bitaxeorg/bitaxeBIRDS/3d/TXB0104RGYR.STEP

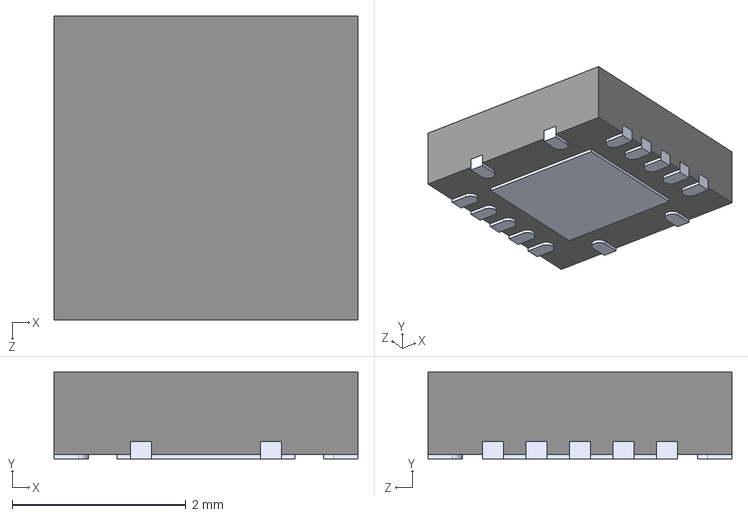
[picture p16: CAD file, 2025-10-02]
3d/TXB0104RGYR.STEP
3.50 x 1.00 x 3.50 mm
