bitaxeorg/bitaxeBIRDS/3d/TPS546D24ARVFR.step

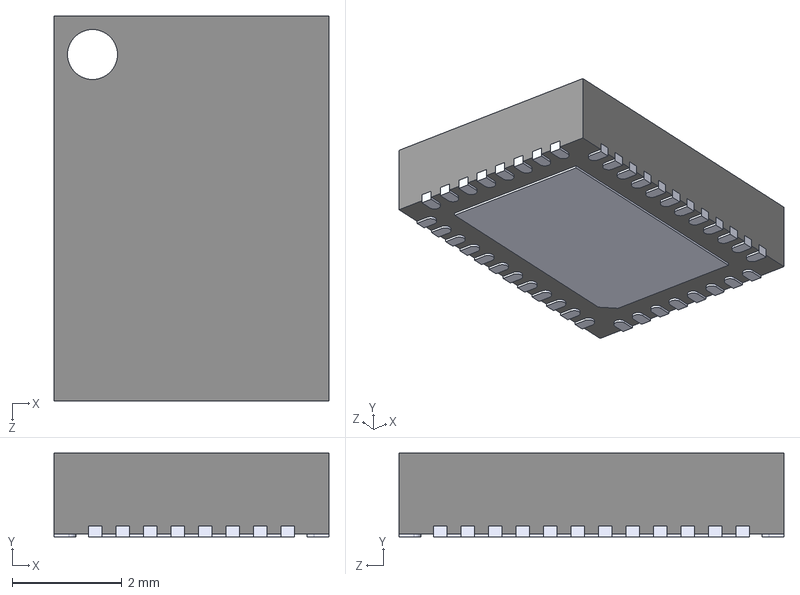
[picture p18: CAD file, 2025-10-02]
3d/TPS546D24ARVFR.step
5.00 x 1.52 x 7.00 mm
