bitaxeorg/bitaxeBIRDS/3d/BitaxeGT_heatsink.step

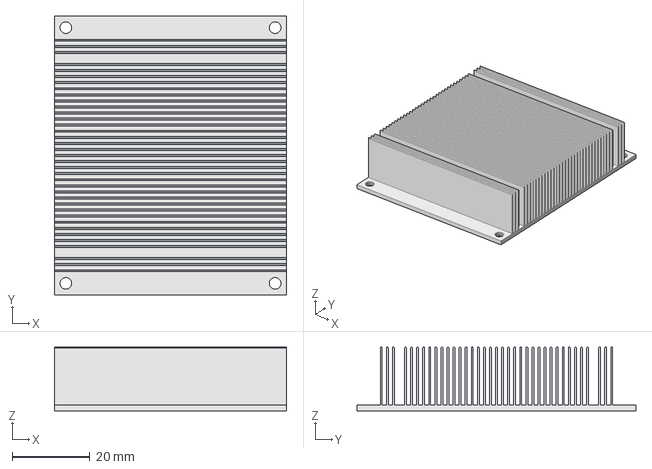
[picture p19: CAD file, 2025-10-02]
3d/BitaxeGT_heatsink.step
60.0 x 72.0 x 16.5 mm
