bitaxeorg/bitaxeBIRDS/3d/BM04B-SRSS-TB.STEP

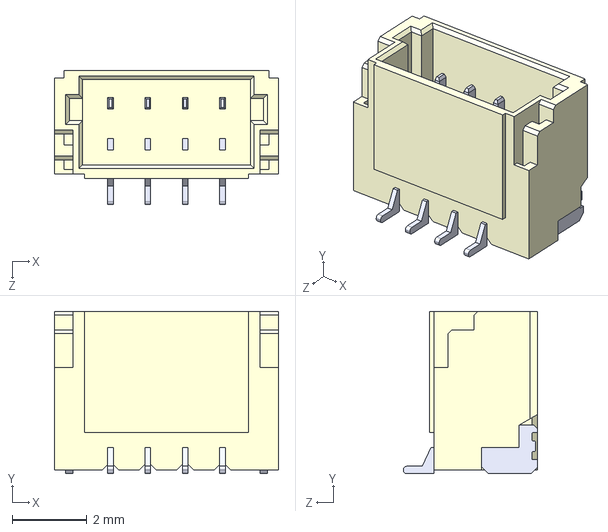
[picture p20: CAD file, 2025-10-02]
3d/BM04B-SRSS-TB.STEP
6.00 x 4.35 x 3.60 mm
