bitaxeorg/bitaxeBIRDS/3d/BM1368xx.stp

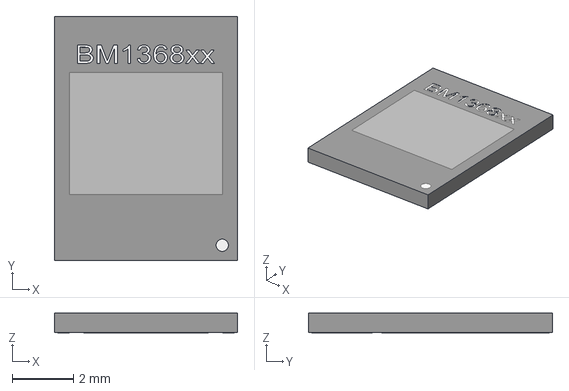
[picture p21: CAD file, 2025-10-02]
3d/BM1368xx.stp
6.00 x 8.00 x 0.65 mm
