bitaxeorg/bitaxeBIRDS/3d/USB_10118193-0001LF.STEP

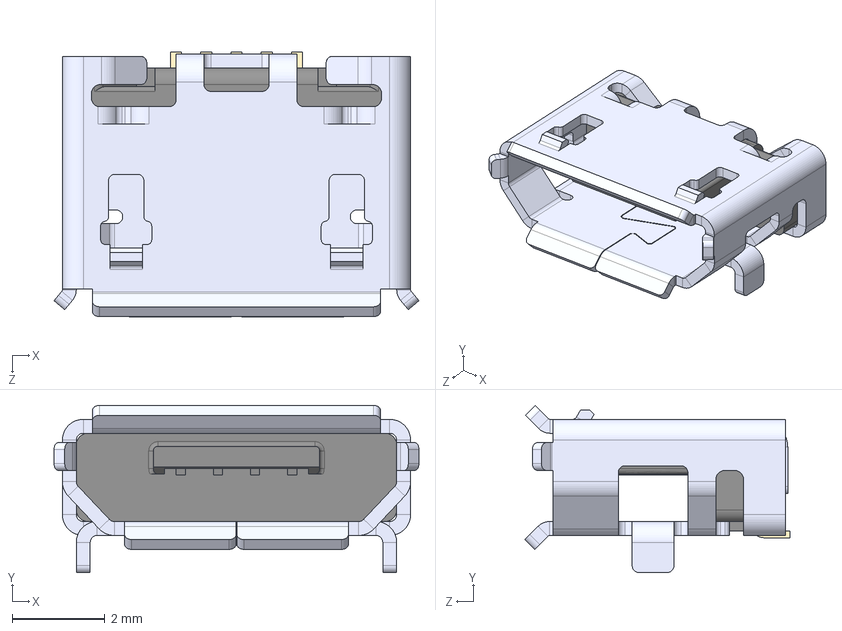
[picture p25: CAD file, 2025-10-02]
3d/USB_10118193-0001LF.STEP
7.86 x 3.60 x 5.71 mm
