bitaxeorg/bitaxeBIRDS/3d/IHLP2020CZ.step

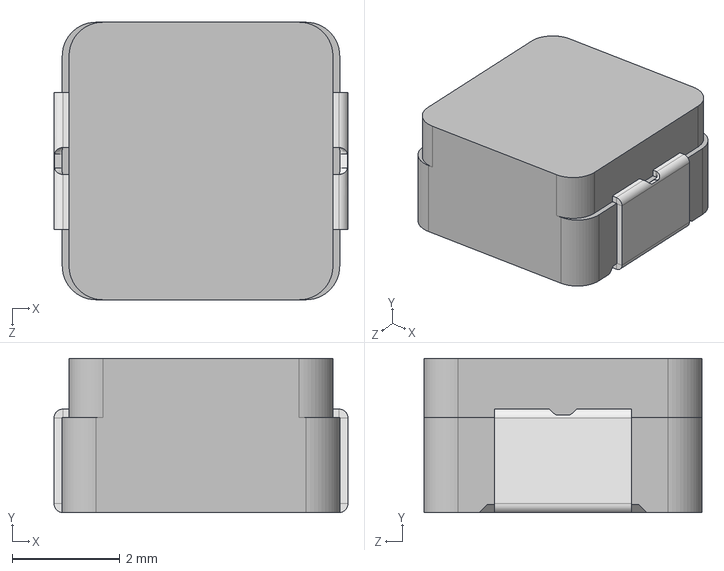
[picture p26: CAD file, 2025-10-02]
3d/IHLP2020CZ.step
5.45 x 2.86 x 5.15 mm
