bitaxeorg/bitaxeBIRDS/3d/TSOT-23-5_RIT.step

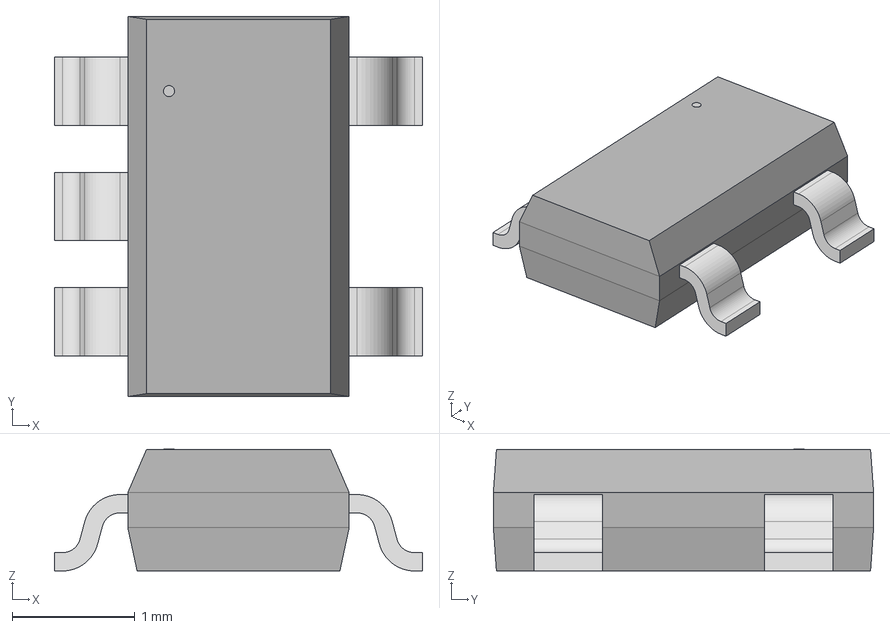
[picture p28: CAD file, 2025-10-02]
3d/TSOT-23-5_RIT.step
3.00 x 3.10 x 0.993 mm
