bitaxeorg/bitaxeBIRDS/3d/FFC2B35-08-T.STEP

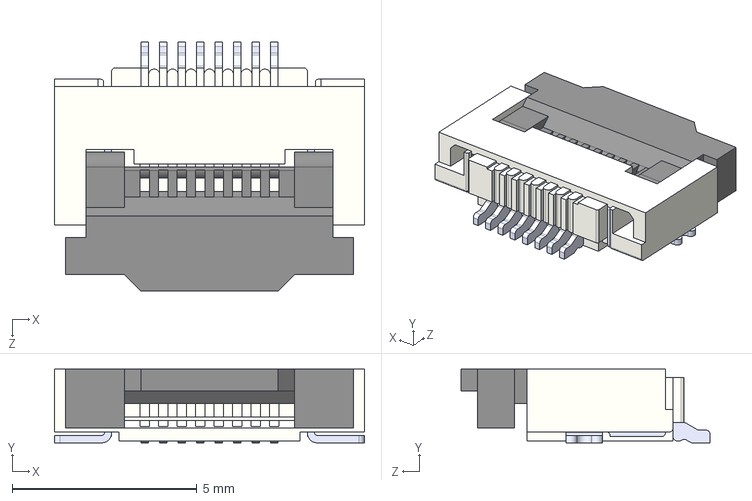
[picture p29: CAD file, 2025-10-02]
3d/FFC2B35-08-T.STEP
8.40 x 2.00 x 6.76 mm
