bitaxeorg/bitaxeBIRDS/3d/DRC0010J.stp

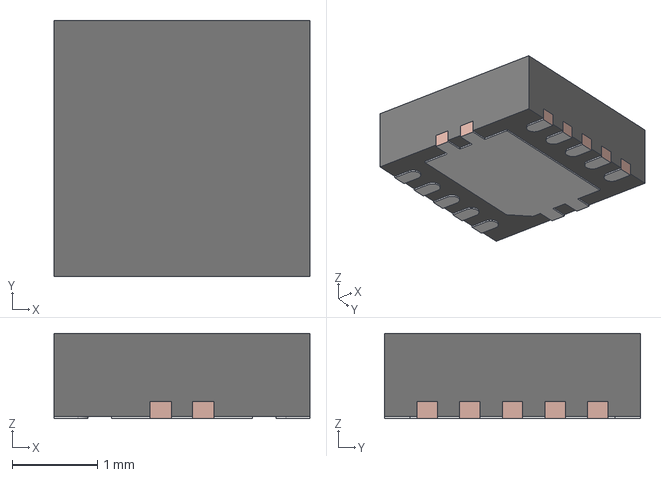
[picture p30: CAD file, 2025-10-02]
3d/DRC0010J.stp
3.00 x 3.00 x 1.00 mm
BODY-SON
FRAME-DRC0010J
