bitaxeorg/bitaxeBIRDS/3d/BQB0016A.stp

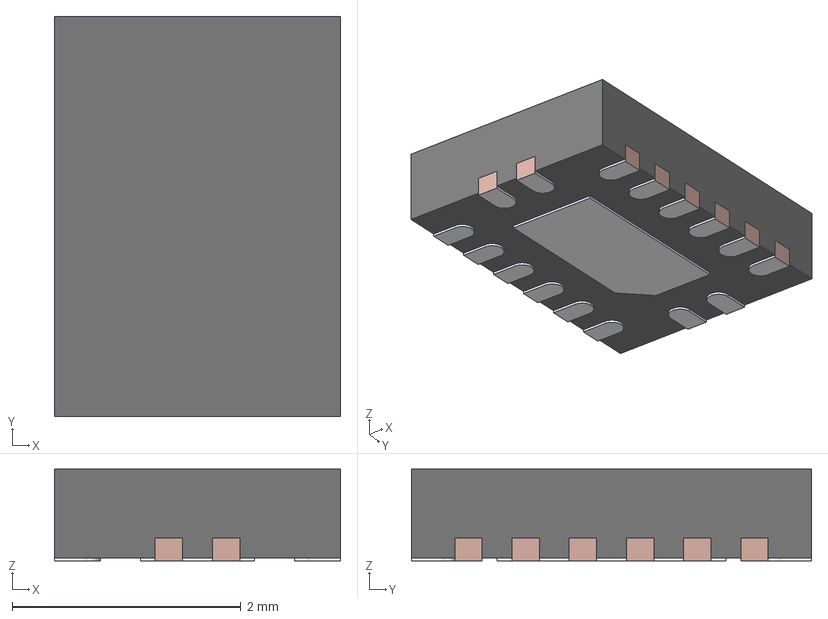
[picture p32: CAD file, 2025-10-02]
3d/BQB0016A.stp
2.50 x 3.50 x 0.8 mm
FRAME
