bitaxeorg/bitaxeBIRDS/3d/GT heatsink.step

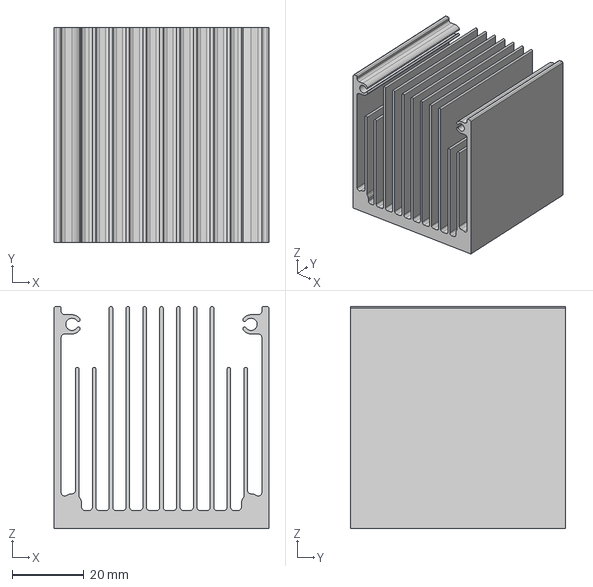
[picture p35: CAD file, 2025-10-02]
3d/GT heatsink.step
60.0 x 60.0 x 62.0 mm
