bitaxeorg/bitaxeBIRDS/3d/DHVQFN14_SOT762-1_NEX.step

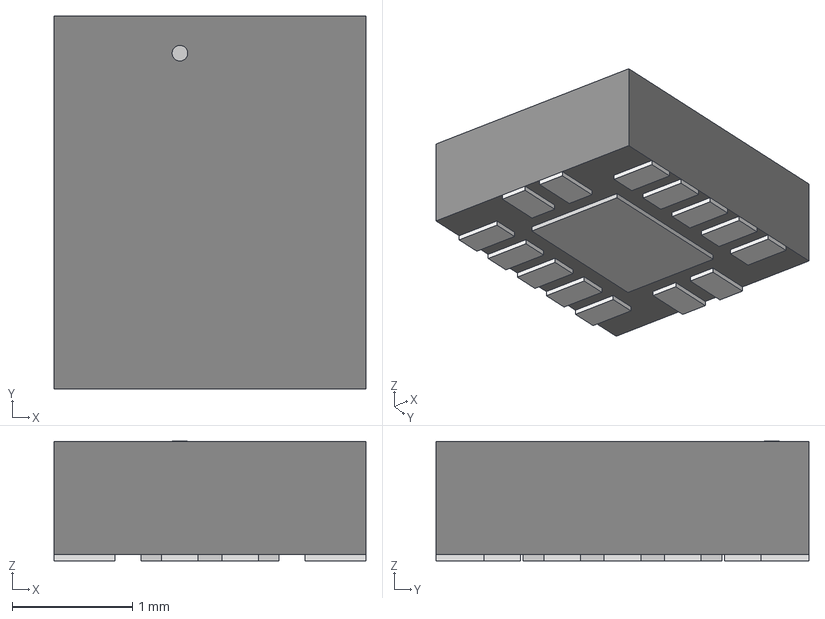
[picture p37: CAD file, 2025-10-02]
3d/DHVQFN14_SOT762-1_NEX.step
2.59 x 3.10 x 0.993 mm
