bitaxeorg/bitaxeBIRDS/3d/Bitaxe_Heatsink.step

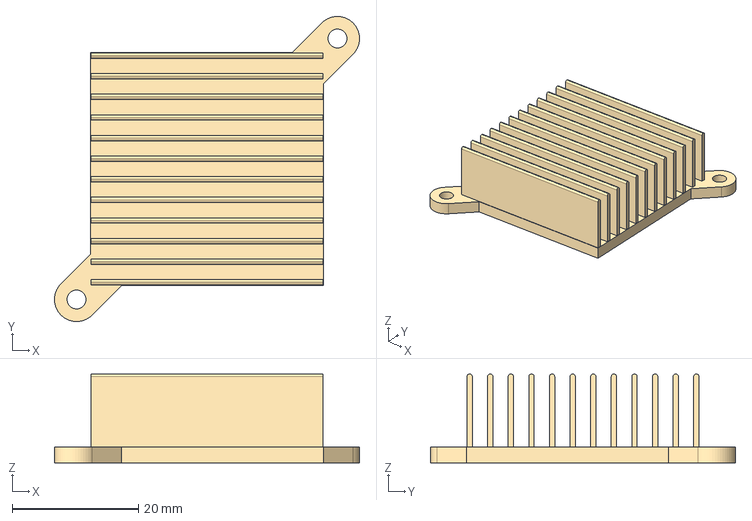
[picture p38: CAD file, 2025-10-02]
3d/Bitaxe_Heatsink.step
48.4 x 48.4 x 14.1 mm
