bitaxeorg/bitaxeBIRDS/3d/oscillator3.2x2.5.step

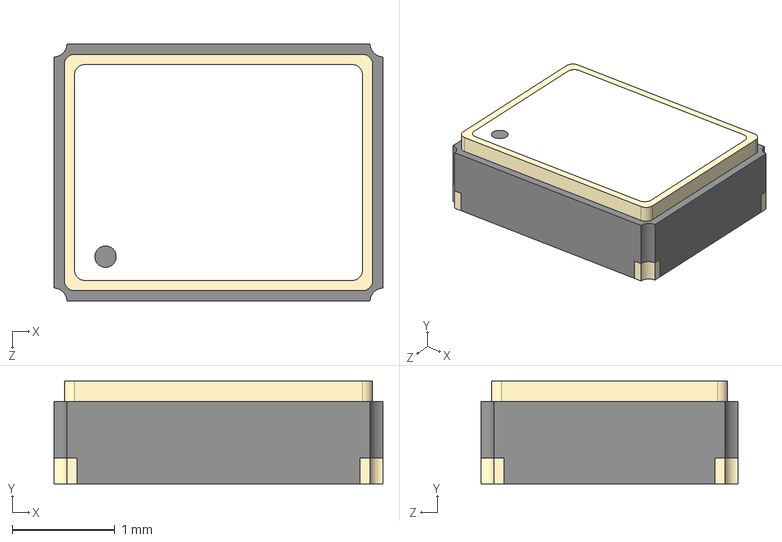
[picture p39: CAD file, 2025-10-02]
3d/oscillator3.2x2.5.step
3.20 x 1.00 x 2.50 mm
