bitaxeorg/bitaxeBIRDS/3d/c-63862-1-r-3d.stp

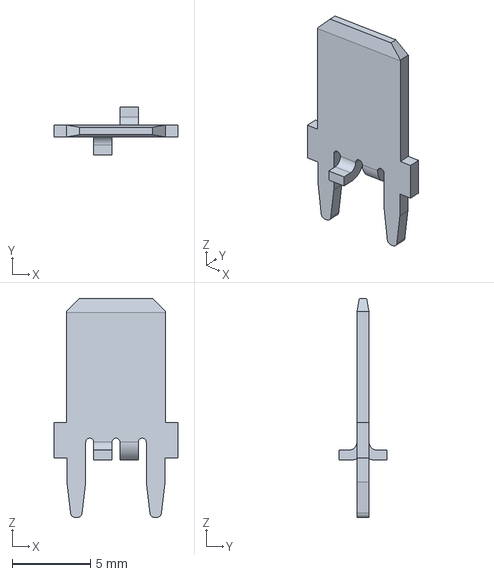
[picture p40: CAD file, 2025-10-02]
3d/c-63862-1-r-3d.stp
7.92 x 3.07 x 14.0 mm
