bitaxeorg/bitaxeBIRDS/3d/CS1213AG-tr.stp

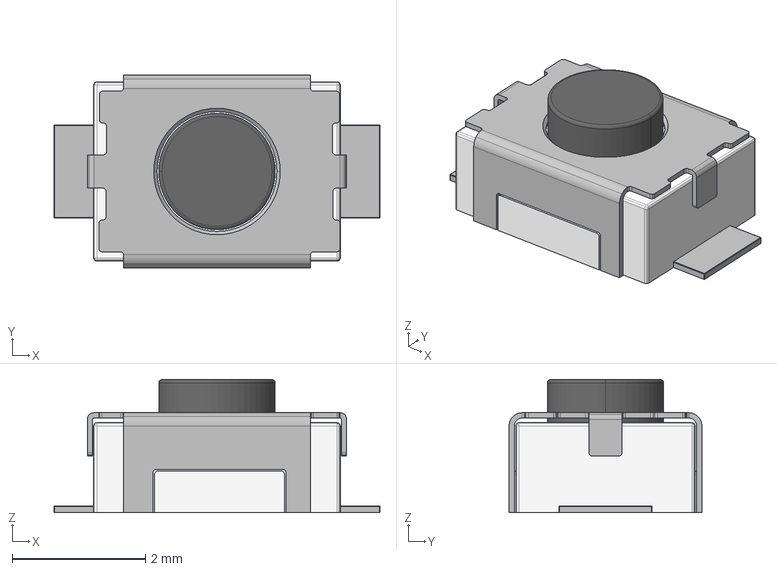
[picture p42: CAD file, 2025-10-02]
3d/CS1213AG-tr.stp
4.90 x 2.90 x 2.00 mm
