bitaxeorg/bitaxeBIRDS/3d/141_TL3330AFxxxQG.stp

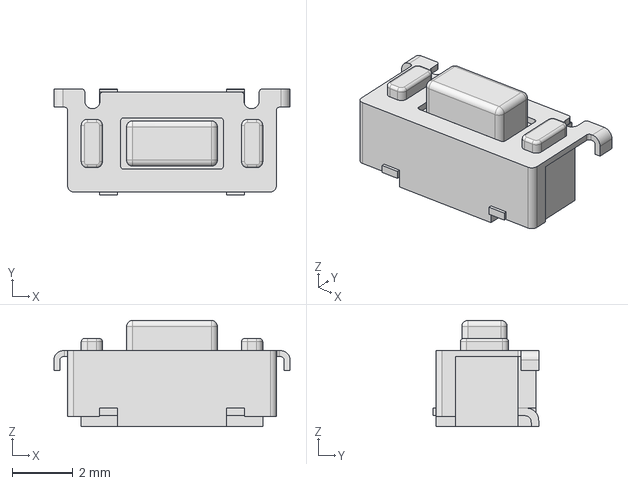
[picture p47: CAD file, 2025-10-02]
3d/141_TL3330AFxxxQG.stp
7.80 x 3.50 x 3.51 mm
