bitaxeorg/bitaxeBIRDS/3d/21-0164B_L622-1_MXM.step

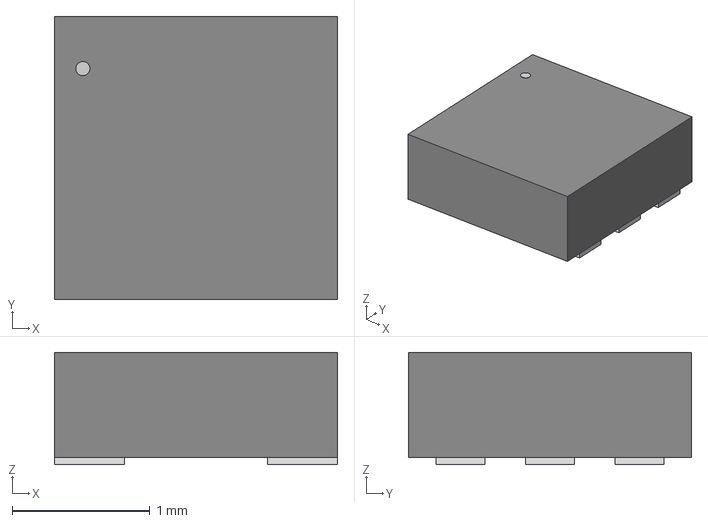
[picture p49: CAD file, 2025-10-02]
3d/21-0164B_L622-1_MXM.step
2.06 x 2.06 x 0.815 mm
