bitaxeorg/bitaxeBIRDS/3d/CUI_DEVICES_PJ-002AH.step

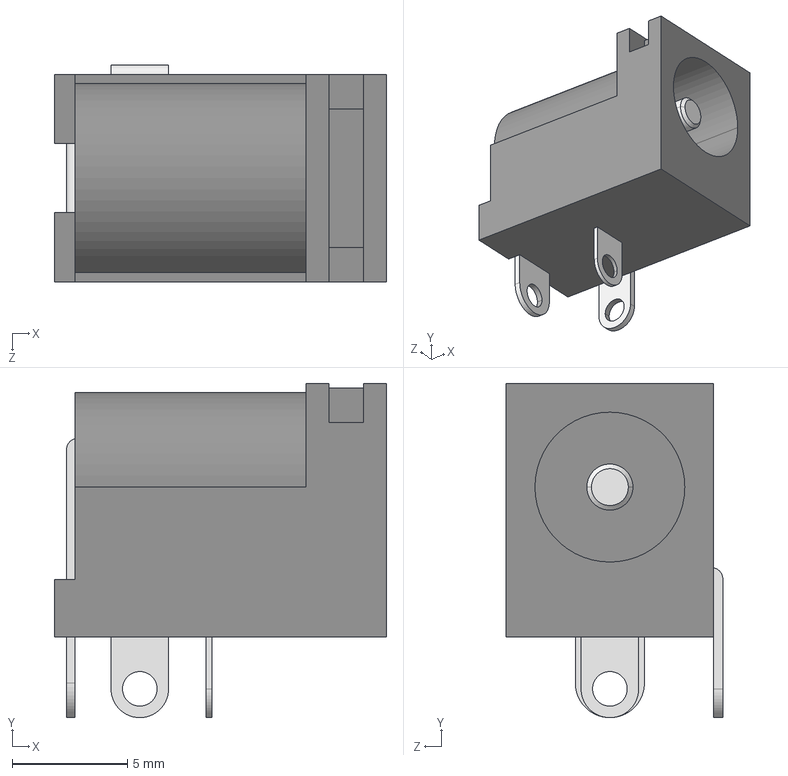
[picture p51: CAD file, 2025-10-02]
3d/CUI_DEVICES_PJ-002AH.step
14.4 x 14.5 x 9.40 mm
