bitaxeorg/bitaxeBIRDS/3d/CUI_DEVICES_PJ-037AH.step

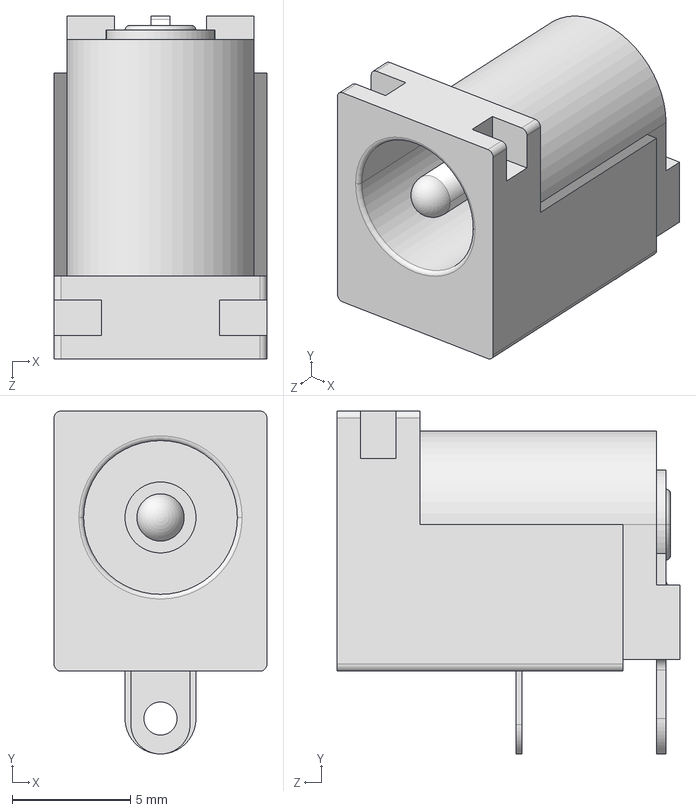
[picture p52: CAD file, 2025-10-02]
3d/CUI_DEVICES_PJ-037AH.step
9.00 x 14.5 x 14.5 mm
