bitaxeorg/bitaxeBIRDS/3d/SMV_z90.stp

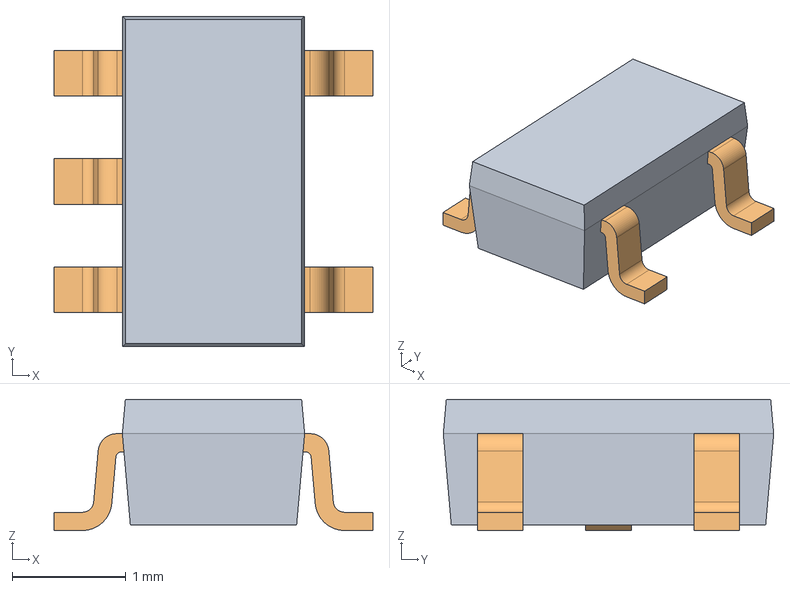
[picture p54: CAD file, 2025-10-02]
3d/SMV_z90.stp
2.80 x 2.90 x 1.15 mm
