bitaxeorg/bitaxeBIRDS/3d/XRCGB27M120F3M10R0_MUR.step

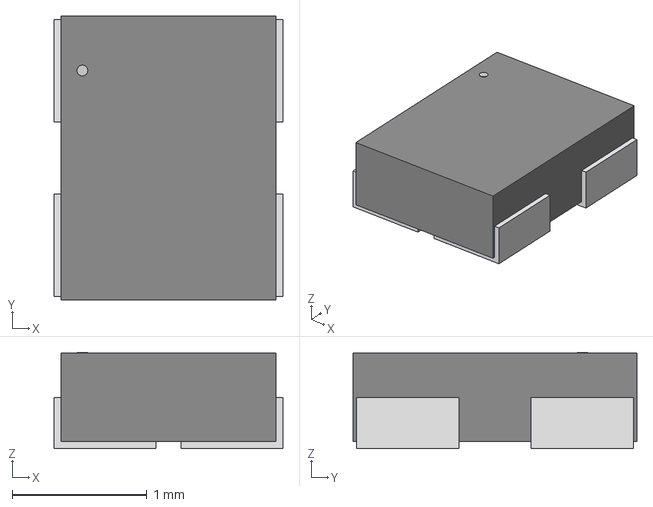
[picture p55: CAD file, 2025-10-02]
3d/XRCGB27M120F3M10R0_MUR.step
1.70 x 2.11 x 0.714 mm
