bitaxeorg/bitaxeBIRDS/3d/FTSH-105-01-F-DV-K.stp

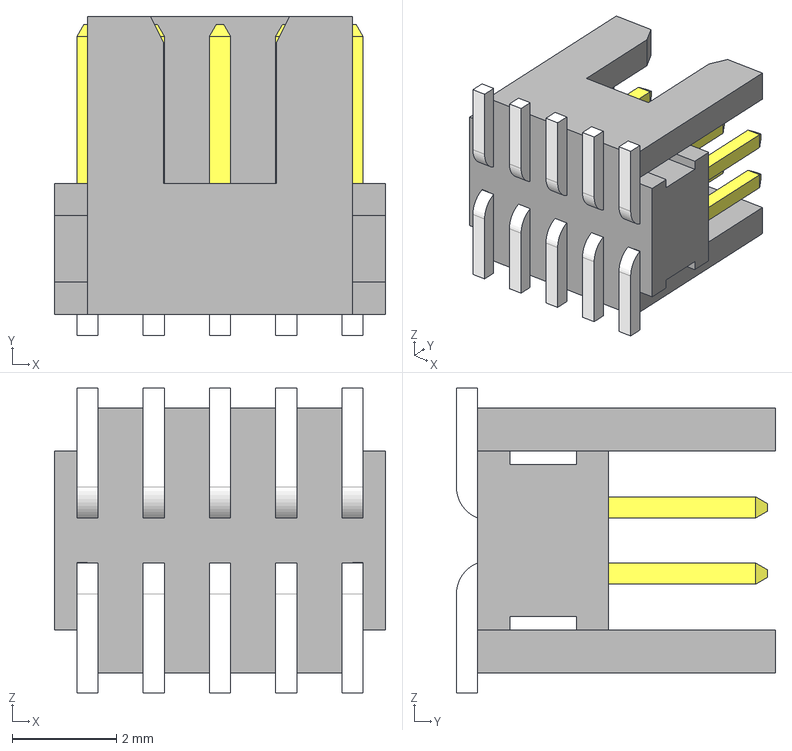
[picture p56: CAD file, 2025-10-02]
3d/FTSH-105-01-F-DV-K.stp
6.35 x 6.12 x 5.84 mm
FTSH-105-01-F-DV-K_pins2
FTSH-105-01-F-DV-K_pins1
FTSH-105-01-F-DV-K_body
