bitaxeorg/bitaxeBIRDS/3d/XT30PW-M.stp

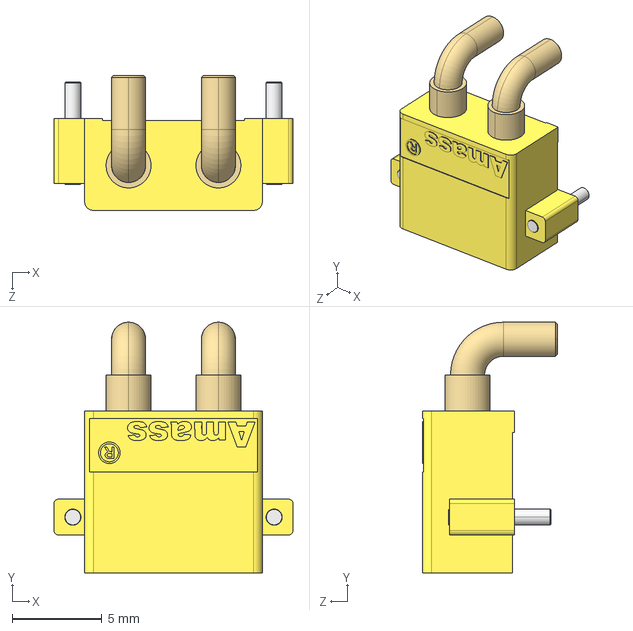
[picture p58: CAD file, 2025-10-02]
3d/XT30PW-M.stp
13.3 x 13.9 x 7.50 mm
