bitaxeorg/bitaxeBIRDS/3d/bm1370.step

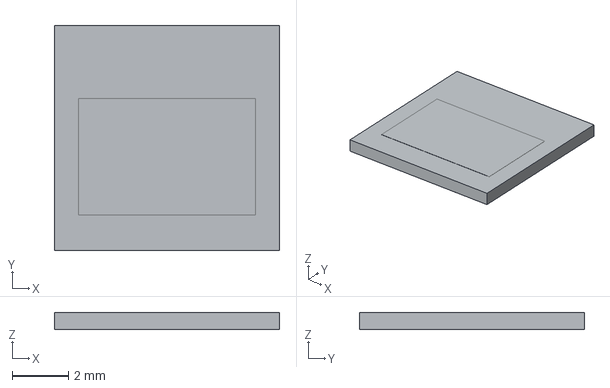
[picture p60: CAD file, 2025-10-02]
3d/bm1370.step
8.00 x 8.00 x 0.61 mm
