bitaxeorg/bitaxeBIRDS/3d/DRL0006A.stp

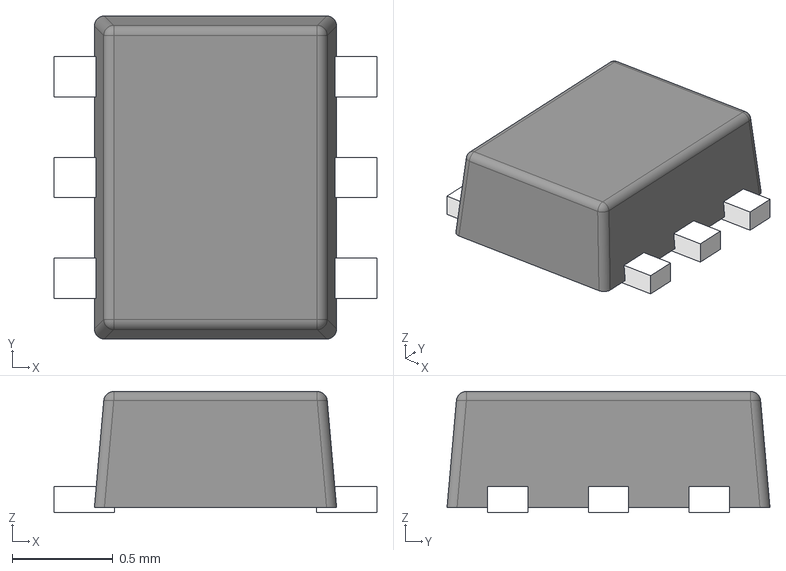
[picture p61: CAD file, 2025-10-02]
3d/DRL0006A.stp
1.60 x 1.60 x 0.6 mm
FRAME-DRL0006A
BODY-SOT
PIN1-ID
