bitaxeorg/bitaxeBIRDS/3d/QFN16_4X4_MCH.step

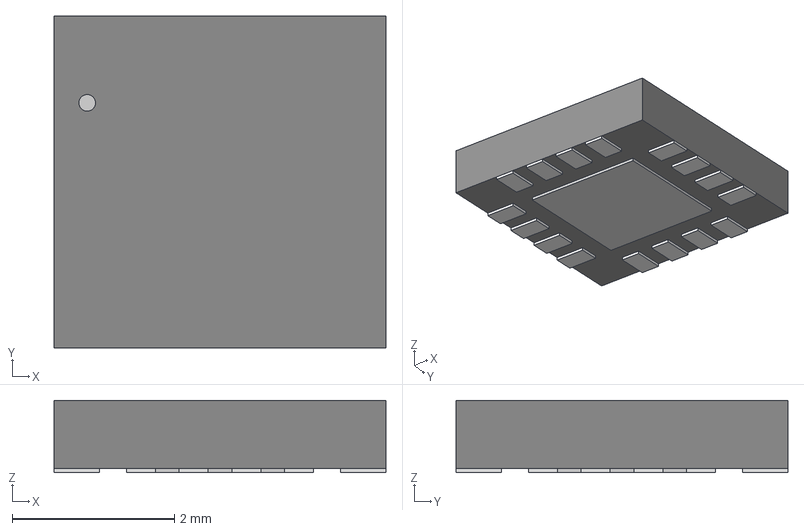
[picture p62: CAD file, 2025-10-02]
3d/QFN16_4X4_MCH.step
4.09 x 4.09 x 0.892 mm
