bitaxeorg/bitaxeBIRDS/3d/SW_CS1213AGF260_CRS.step

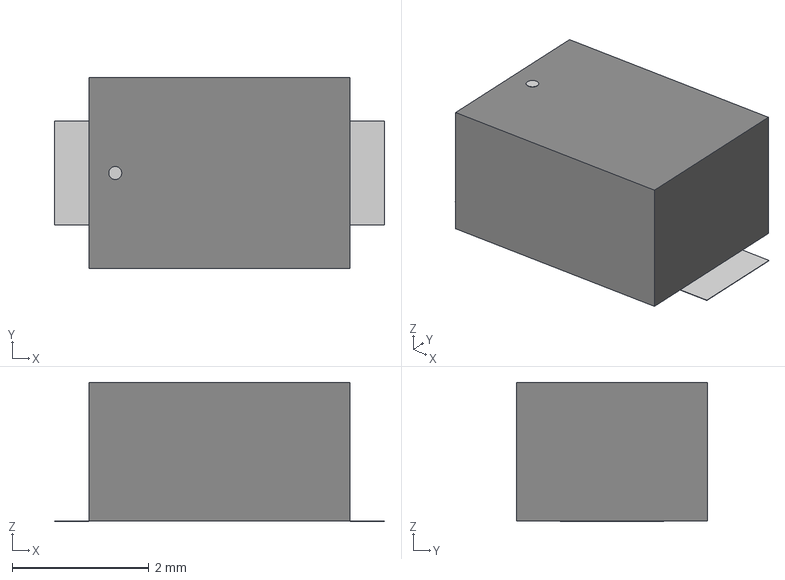
[picture p64: CAD file, 2025-10-02]
3d/SW_CS1213AGF260_CRS.step
4.83 x 2.79 x 2.04 mm
