bitaxeorg/bitaxeBIRDS/3d/Coilcraft-SLC1175.STEP

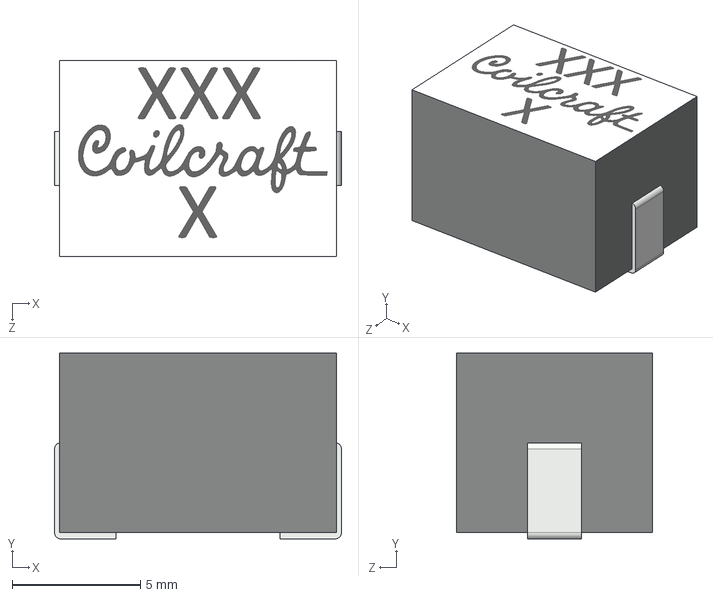
[picture p65: CAD file, 2025-10-02]
3d/Coilcraft-SLC1175.STEP
11.2 x 7.25 x 7.65 mm
